sensemakersamsterdam/xmas2024/kicad/kerstboom.kicad_sch

## KiCad design kicad/kerstboom.kicad_sch (2024-11-24)

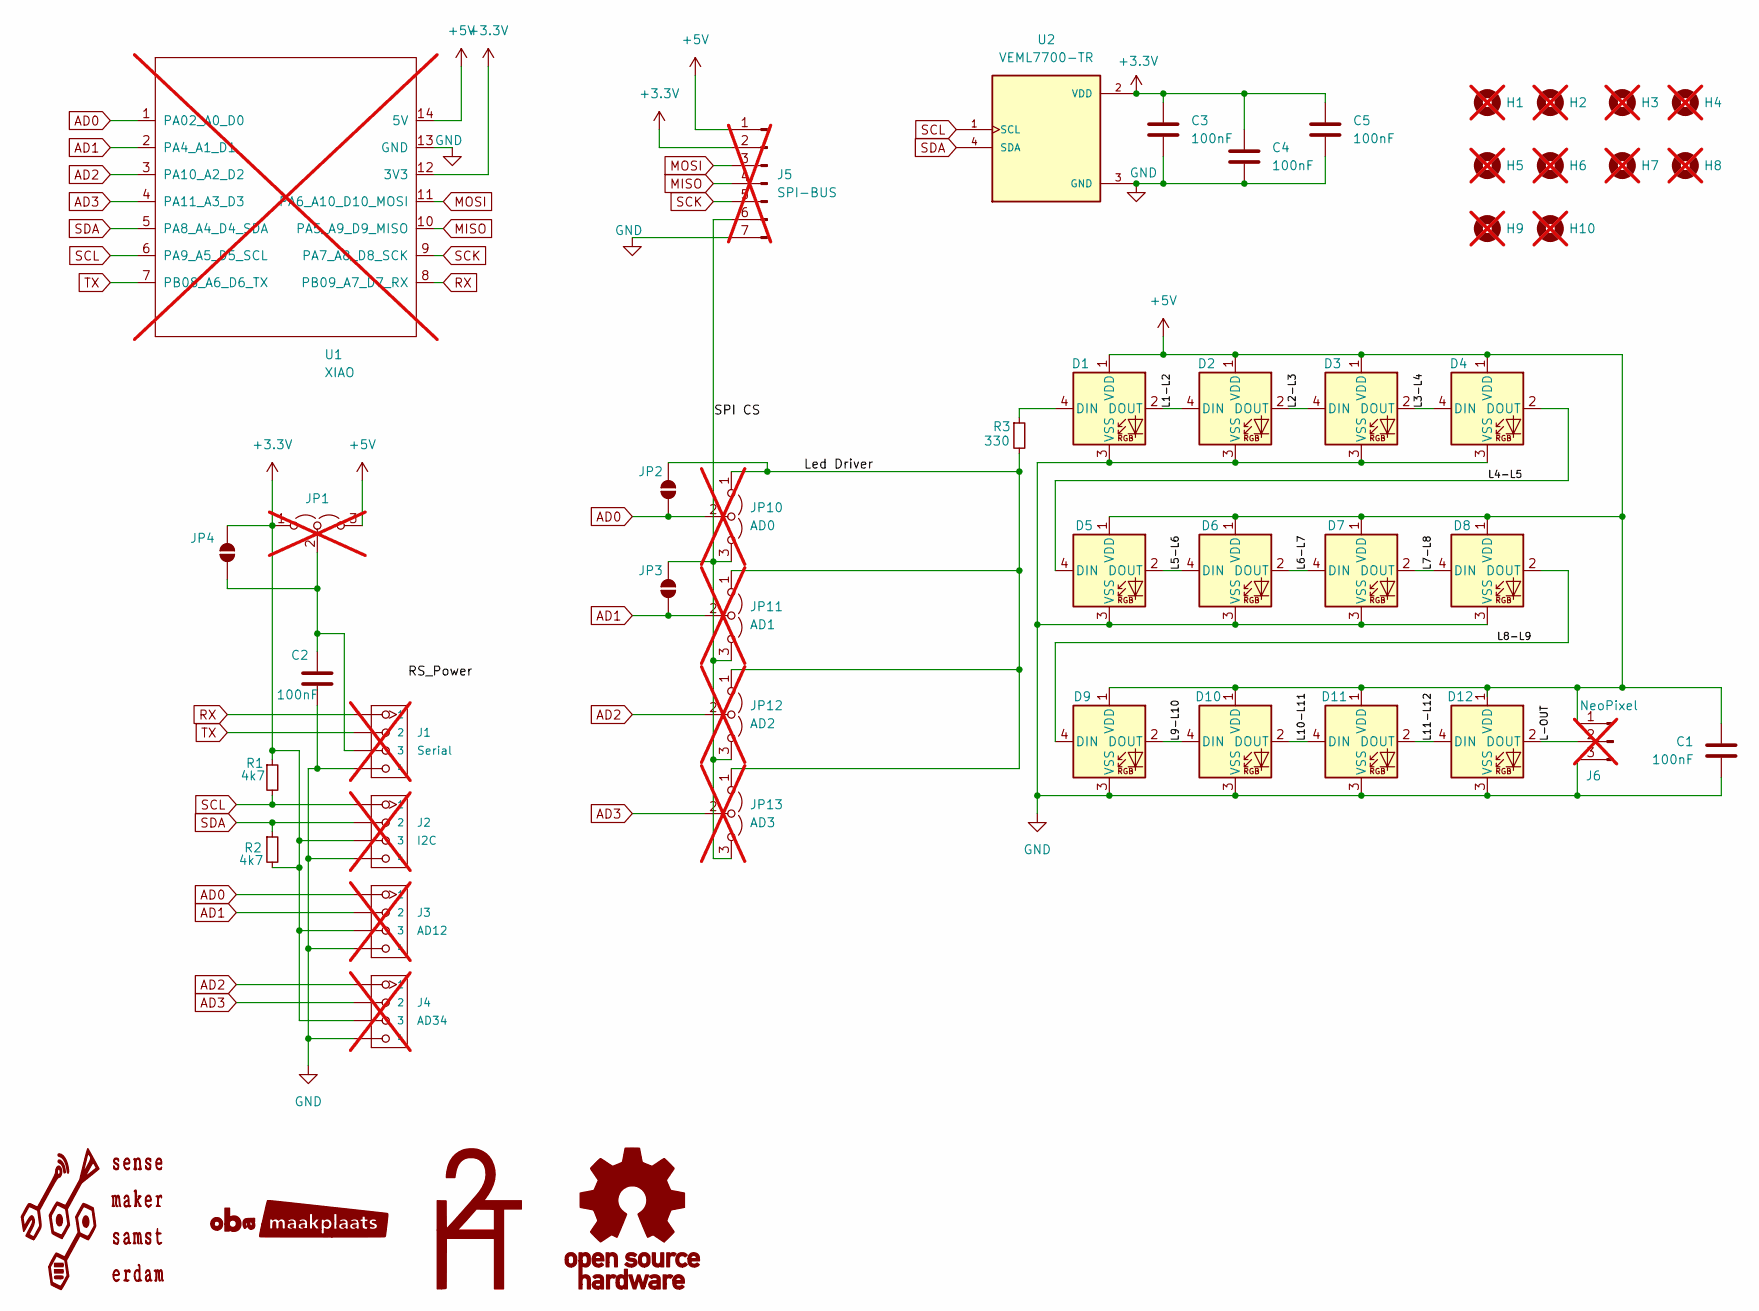
[picture p26: schematic kerstboom.kicad_sch]

Parts:
C1, C2, C3, C4, C5: 100nF; C_0805_2012Metric; JLC C49678
D1, D2, D3, D4, D5, D6, D7, D8, D9, D10, D11, D12: WS2812B; LED_WS2812B_PLCC4_5.0x5.0mm_P3.2mm; JLC C2874885
H1, H2, H3, H4: MountingHole; MountingHole_3.2mm_M3; not fitted
H5, H6, H7, H8, H9, H10: MountingHole; MountingHole_2.2mm_M2; not fitted
J1: Serial; GROVE-HW4-2.0-90D; not fitted
J2: I2C; GROVE-HW4-2.0-90D; not fitted
J3: AD12; GROVE-HW4-2.0-90D; not fitted
J4: AD34; GROVE-HW4-2.0-90D; not fitted
J5: SPI-BUS; PinHeader_1x07_P2.54mm_Vertical; not fitted
J6: NeoPixel; PinHeader_1x03_P2.54mm_Vertical; not fitted
JP1: Jumper_3_Open; PinHeader_1x03_P2.54mm_Vertical; not fitted
JP2, JP3, JP4: SolderJumper_2_Open; SolderJumper-2_P1.3mm_Open_Pad1.0x1.5mm
JP10: AD0; PinHeader_1x03_P2.54mm_Vertical; not fitted
JP11: AD1; PinHeader_1x03_P2.54mm_Vertical; not fitted
JP12: AD2; PinHeader_1x03_P2.54mm_Vertical; not fitted
JP13: AD3; PinHeader_1x03_P2.54mm_Vertical; not fitted
R1, R2: 4k7; R_0805_2012Metric_Pad1.20x1.40mm_HandSolder; JLC C17673
R3: 330; R_0805_2012Metric_Pad1.20x1.40mm_HandSolder; JLC C17630
U1: XIAO; Seeeduino XIAO-MOUDLE14P-2.54-21X17.8MM-holes; not fitted
U2: VEML7700-TR; XDCR_VEML7700-TR; PARTREV 1.6; JLC C504893

Connections:
+3.3V: C3.1, C4.1, C5.1, J2.3, J3.3, J4.3, J5.2, JP1.1 (A), JP4.2 (B), R1.1, R2.2, U1.12 (3V3), U2.2 (VDD)
+5V: C1.1, D1.1 (VDD), D2.1 (VDD), D3.1 (VDD), D4.1 (VDD), D5.1 (VDD), D6.1 (VDD), D7.1 (VDD), D8.1 (VDD), D9.1 (VDD), D10.1 (VDD), D11.1 (VDD), D12.1 (VDD), J5.1, J6.1, JP1.3 (B), U1.14 (5V)
AD0: J3.1, JP2.1 (A), JP10.2 (C), U1.1 (PA02_A0_D0)
AD1: J3.2, JP3.1 (A), JP11.2 (C), U1.2 (PA4_A1_D1)
AD2: J4.1, JP12.2 (C), U1.3 (PA10_A2_D2)
AD3: J4.2, JP13.2 (C), U1.4 (PA11_A3_D3)
GND: C1.2, C2.2, C3.2, C4.2, C5.2, D1.3 (VSS), D2.3 (VSS), D3.3 (VSS), D4.3 (VSS), D5.3 (VSS), D6.3 (VSS), D7.3 (VSS), D8.3 (VSS), D9.3 (VSS), D10.3 (VSS), D11.3 (VSS), D12.3 (VSS), J1.4, J2.4, J3.4, J4.4, J5.7, J6.3, U1.13 (GND), U2.3 (GND)
L1-L2: D1.2 (DOUT), D2.4 (DIN)
L2-L3: D2.2 (DOUT), D3.4 (DIN)
L3-L4: D3.2 (DOUT), D4.4 (DIN)
L4-L5: D4.2 (DOUT), D5.4 (DIN)
L5-L6: D5.2 (DOUT), D6.4 (DIN)
L6-L7: D6.2 (DOUT), D7.4 (DIN)
L7-L8: D7.2 (DOUT), D8.4 (DIN)
L8-L9: D8.2 (DOUT), D9.4 (DIN)
L9-L10: D9.2 (DOUT), D10.4 (DIN)
L10-L11: D10.2 (DOUT), D11.4 (DIN)
L11-L12: D11.2 (DOUT), D12.4 (DIN)
L-OUT: D12.2 (DOUT), J6.2
Led Driver: JP2.2 (B), JP10.1 (A), JP11.1 (A), JP12.1 (A), JP13.1 (A), R3.2
MISO: J5.4, U1.10 (PA5_A9_D9_MISO)
MOSI: J5.3, U1.11 (PA6_A10_D10_MOSI)
unnamed: C2.1, J1.3, JP1.2 (C), JP4.1 (A)
unnamed: D1.4 (DIN), R3.1
RX: J1.1, U1.8 (PB09_A7_D7_RX)
SCK: J5.5, U1.9 (PA7_A8_D8_SCK)
SCL: J2.1, R1.2, U1.6 (PA9_A5_D5_SCL), U2.1 (SCL)
SDA: J2.2, R2.1, U1.5 (PA8_A4_D4_SDA), U2.4 (SDA)
SPI CS: J5.6, JP3.2 (B), JP10.3 (B), JP11.3 (B), JP12.3 (B), JP13.3 (B)
TX: J1.2, U1.7 (PB08_A6_D6_TX)
